wivy1/KeyLED/electronics/keyled_circuit.sch

## KiCad design electronics/keyled_circuit.sch (2025-03-23)

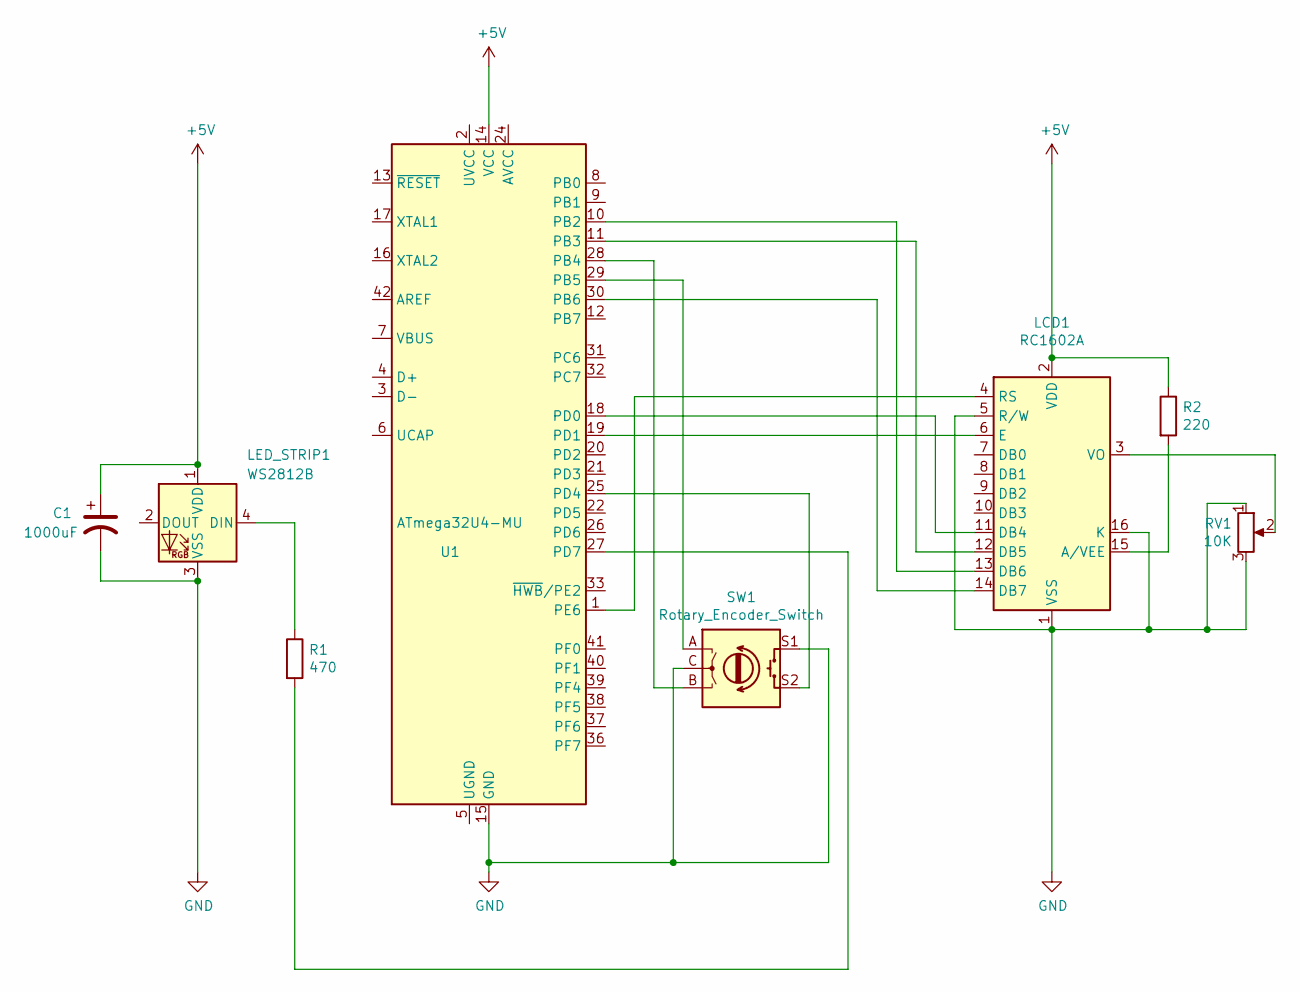
[picture p10: schematic keyled_circuit.sch]

Parts:
C1: 1000uF
LCD1: RC1602A
LED_STRIP1: WS2812B; LED_WS2812B_PLCC4_5.0x5.0mm_P3.2mm
R1: 470
R2: 220
RV1: 10K
SW1: Rotary_Encoder_Switch
U1: ATmega32U4-MU; QFN-44-1EP_7x7mm_P0.5mm_EP5.2x5.2mm

Connections:
+5V: C1.1, LCD1.2 (VDD), LED_STRIP1.1 (VDD), R2.1, U1.14 (VCC), U1.34 (VCC)
GND: C1.2, LCD1.1 (VSS), LCD1.5 (R/W), LCD1.16 (K), LED_STRIP1.3 (VSS), RV1.1, RV1.3, SW1.C, SW1.S1, U1.15 (GND), U1.23 (GND), U1.35 (GND), U1.43 (GND), U1.45 (GND)
unnamed: LCD1.3 (VO), RV1.2
unnamed: LCD1.4 (RS), U1.1 (PE6)
unnamed: LCD1.6 (E), U1.19 (PD1)
unnamed: LCD1.11 (DB4), U1.18 (PD0)
unnamed: LCD1.12 (DB5), U1.11 (PB3)
unnamed: LCD1.13 (DB6), U1.10 (PB2)
unnamed: LCD1.14 (DB7), U1.30 (PB6)
unnamed: LCD1.15 (A/VEE), R2.2
unnamed: LED_STRIP1.4 (DIN), R1.1
unnamed: R1.2, U1.27 (PD7)
unnamed: SW1.A, U1.29 (PB5)
unnamed: SW1.B, U1.28 (PB4)
unnamed: SW1.S2, U1.25 (PD4)
unnamed: U1.24 (AVCC), U1.44 (AVCC)
